SshgurkiratSingh/CCMS_PORTAL/Firmware/STM32_Peripheral/src/meter_handler.cpp

#include "meter_handler.h"
#include <Arduino.h>

void MeterHandler::init() {
    // Initialize Modbus UART (Serial2 or similar)
    // Setup for RS485 communication
}

MeterData MeterHandler::readRegisters() {
    MeterData data;
    
    // Stub: Replace with actual Modbus RTU reading logic
    // matching the old ESP32 meter_handler.cpp
    data.voltage = 230.5;
    data.current = 1.2;
    data.power = 276.6;
    data.energy = 1500.0;
    
    return data;
}
