SshgurkiratSingh/CCMS_PORTAL/Firmware/ESP32_wifi_CCMS_v2.0/include/mqtt_handler.h

#ifndef MQTT_HANDLER_H
#define MQTT_HANDLER_H

#include <PubSubClient.h>

extern PubSubClient mqttClient;

void setupMQTT();
void handleMQTTConnection();
void publishMqttData();
void mqttCallback(char *topic, byte *payload, unsigned int length);

#endif
